ZelTroN-2k3/firmware-macropad.ESP-32/icondata.h

/* ---------------------------------------------------------------------- */
/* -------------------- BITMAPS (stockés en PROGMEM) -------------------- */
/* ---------------------------------------------------------------------- */

#pragma once

// =============================================================================
//     BIBLIOTHEQUE D'ICONES
// =============================================================================
// Ce fichier contient les données brutes (bitmaps) de toutes les icônes
// utilisées dans le projet. Elles sont stockées en PROGMEM pour économiser la RAM.
// -----------------------------------------------------------------------------

// Sur ESP32, le simple fait de déclarer un tableau en 'const'
// le place en mémoire Flash. PROGMEM n'est plus requis.

// --- ICONES POUR LE MENU DE DÉMARRAGE (16x16 pixels) ---
const unsigned char icon_menu_pc_16x16[]          PROGMEM = { 0x00, 0x00, 0x00, 0x00, 0x00, 0x00, 0x3f, 0xfc, 0x3f, 0xfc, 0x30, 0x0c, 0x30, 0x0c, 0x30, 0x0c, 0x30, 0x0c, 0x3f, 0xfc, 0x3f, 0xfc, 0x01, 0x80, 0x07, 0xe0, 0x0f, 0xf0, 0x00, 0x00, 0x00, 0x00, };
const unsigned char icon_menu_souris_16x16[]      PROGMEM = { 0x00, 0x00, 0x00, 0x00, 0x00, 0x00, 0x06, 0xc0, 0x0c, 0x60, 0x0d, 0x60, 0x0d, 0x60, 0x01, 0x00, 0x0c, 0x60, 0x0f, 0xe0, 0x0f, 0xe0, 0x07, 0xc0, 0x03, 0x80, 0x00, 0x00, 0x00, 0x00, 0x00, 0x00, };
const unsigned char icon_menu_clavier_16x16[]     PROGMEM = { 0x00, 0x00, 0x00, 0x00, 0x00, 0x00, 0x7f, 0xfc, 0x55, 0x54, 0x7f, 0xfc, 0x6a, 0xac, 0x7f, 0xfc, 0x55, 0x54, 0x7f, 0xfc, 0x60, 0x0c, 0x7f, 0xfc, 0x00, 0x00, 0x00, 0x00, 0x00, 0x00, 0x00, 0x00, };
const unsigned char icon_menu_audio_16x16[]       PROGMEM = { 0x00, 0x00, 0x00, 0x00, 0x00, 0x00, 0x0c, 0x00, 0x1b, 0x00, 0x10, 0x80, 0x10, 0x40, 0x1b, 0x20, 0x19, 0x90, 0x0c, 0x90, 0x26, 0x08, 0x33, 0x98, 0x19, 0xf0, 0x0c, 0x00, 0x00, 0x00, 0x00, 0x00, };
const unsigned char icon_menu_wifi_16x16[]        PROGMEM = { 0x00, 0x00, 0x07, 0xe0, 0x08, 0x10, 0x13, 0xc8, 0x24, 0x24, 0x09, 0x90, 0x02, 0x40, 0x00, 0x00, 0x01, 0x80, 0x00, 0x00, 0x3f, 0xfc, 0x2a, 0xbc, 0x3f, 0xfc, 0x3f, 0xfc, 0x18, 0x18, 0x00, 0x00, };
const unsigned char icon_menu_bluetooth_16x16[]   PROGMEM = { 0x00, 0x00, 0x04, 0x00, 0x06, 0x00, 0x07, 0x10, 0x25, 0x88, 0x37, 0x24, 0x1e, 0x14, 0x0c, 0x14, 0x1e, 0x14, 0x37, 0x24, 0x25, 0x88, 0x07, 0x10, 0x06, 0x00, 0x04, 0x00, 0x00, 0x00, 0x00, 0x00, };
const unsigned char icon_menu_macros_16x16[]      PROGMEM = { 0x00, 0x00, 0x00, 0x00, 0x08, 0x00, 0x0c, 0x00, 0x0e, 0x00, 0x0f, 0x00, 0x0f, 0x80, 0x0f, 0xc0, 0x0f, 0xe0, 0x0f, 0xf0, 0x0f, 0x80, 0x0d, 0x80, 0x08, 0xc0, 0x00, 0xc0, 0x00, 0x00, 0x00, 0x00, };
const unsigned char icon_menu_parametres_16x16[]  PROGMEM = { 0x00, 0x00, 0x00, 0x00, 0x00, 0x00, 0x00, 0x70, 0x00, 0xe0, 0x00, 0xc8, 0x00, 0xf8, 0x01, 0xf0, 0x03, 0xc0, 0x07, 0x80, 0x1f, 0x00, 0x16, 0x00, 0x1c, 0x00, 0x00, 0x00, 0x00, 0x00, 0x00, 0x00, };

// Icône Layer (0,1,2,3) 16x16 pixels
const unsigned char icon_layer_0_16x16[]          PROGMEM = { 0x00, 0x00, 0x00, 0x00, 0x00, 0x00, 0x00, 0x00, 0x03, 0xc0, 0x07, 0xe0, 0x0e, 0x70, 0x0d, 0xb0, 0x0d, 0xb0, 0x0e, 0x70, 0x07, 0xe0, 0x03, 0xc0, 0x00, 0x00, 0x00, 0x00, 0x00, 0x00, 0x00, 0x00, };
const unsigned char icon_layer_1_16x16[]          PROGMEM = { 0x00, 0x00, 0x00, 0x00, 0x00, 0x00, 0x00, 0x00, 0x03, 0xc0, 0x07, 0xe0, 0x0f, 0x70, 0x0e, 0x70, 0x0f, 0x70, 0x0f, 0x70, 0x07, 0xe0, 0x03, 0xc0, 0x00, 0x00, 0x00, 0x00, 0x00, 0x00, 0x00, 0x00, };
const unsigned char icon_layer_2_16x16[]          PROGMEM = { 0x00, 0x00, 0x00, 0x00, 0x00, 0x00, 0x00, 0x00, 0x03, 0xc0, 0x07, 0xe0, 0x0e, 0x70, 0x0f, 0x70, 0x0e, 0xf0, 0x0e, 0x70, 0x07, 0xe0, 0x03, 0xc0, 0x00, 0x00, 0x00, 0x00, 0x00, 0x00, 0x00, 0x00, };
const unsigned char icon_layer_3_16x16[]          PROGMEM = { 0x00, 0x00, 0x00, 0x00, 0x00, 0x00, 0x00, 0x00, 0x03, 0xc0, 0x07, 0xe0, 0x0c, 0xf0, 0x0e, 0x70, 0x0f, 0x70, 0x0e, 0x70, 0x07, 0xe0, 0x03, 0xc0, 0x00, 0x00, 0x00, 0x00, 0x00, 0x00, 0x00, 0x00, };

// Icône Mute 16x16 pixels
const unsigned char icon_mute_16x16[]             PROGMEM = { 0x00, 0x00, 0x00, 0x00, 0x00, 0x00, 0x02, 0x00, 0x06, 0x00, 0x0e, 0x44, 0x3e, 0x28, 0x3e, 0x10, 0x3e, 0x28, 0x3e, 0x44, 0x0e, 0x00, 0x06, 0x00, 0x02, 0x00, 0x00, 0x00, 0x00, 0x00,  0x00, 0x00, };

// Icône Sound 16x16 pixels
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

// Ajoutez vos autres icônes ici...

/* ------------------------------ Fin du code -------------------------------- */
